josephbakarji/Gluvn/docs/gluvn_dataflow.pdf

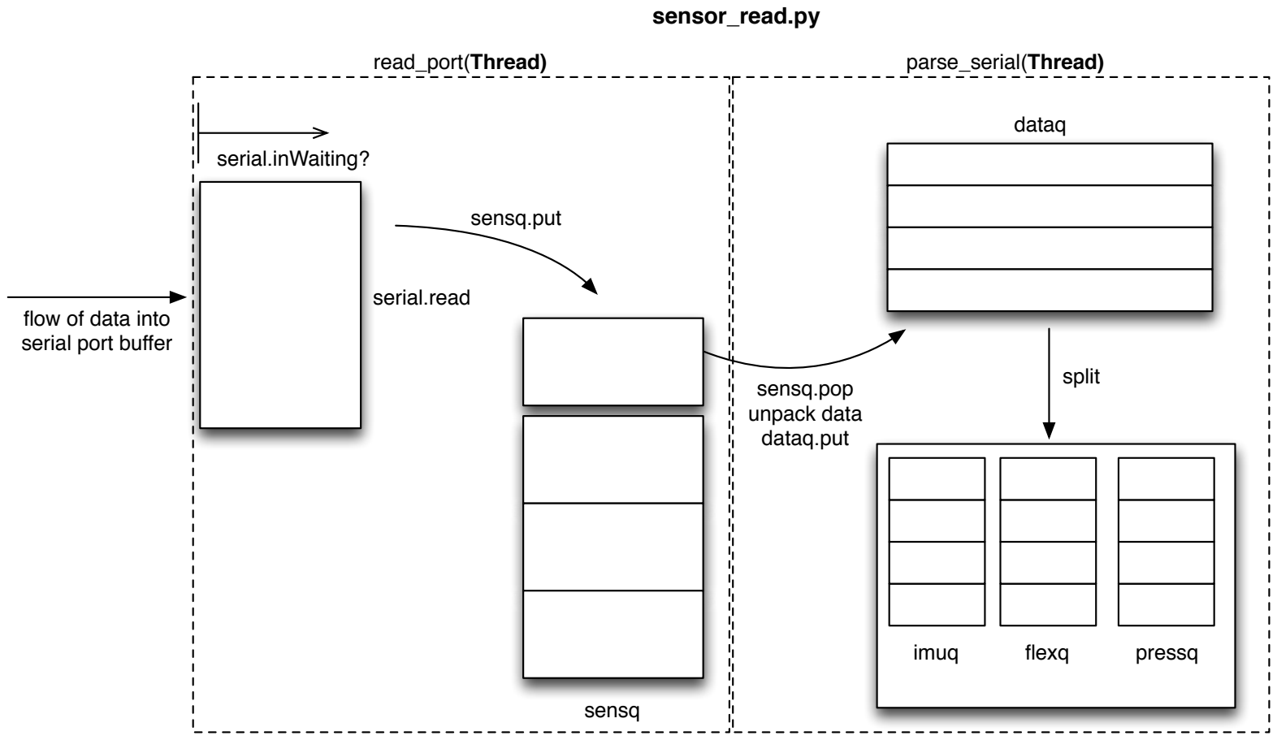
[picture p6: page 1]

flow of data into
serial port buffer

serial.read

sensq.put

sensq

dataq

imuq | flexq | pressq

sensq.pop
unpack data
dataq.put

split

read_port(Thread) | parse_serial(Thread)

sensor_read.py

serial.inWaiting?
