josephbakarji/Gluvn/docs/m5stick_dimensions.png

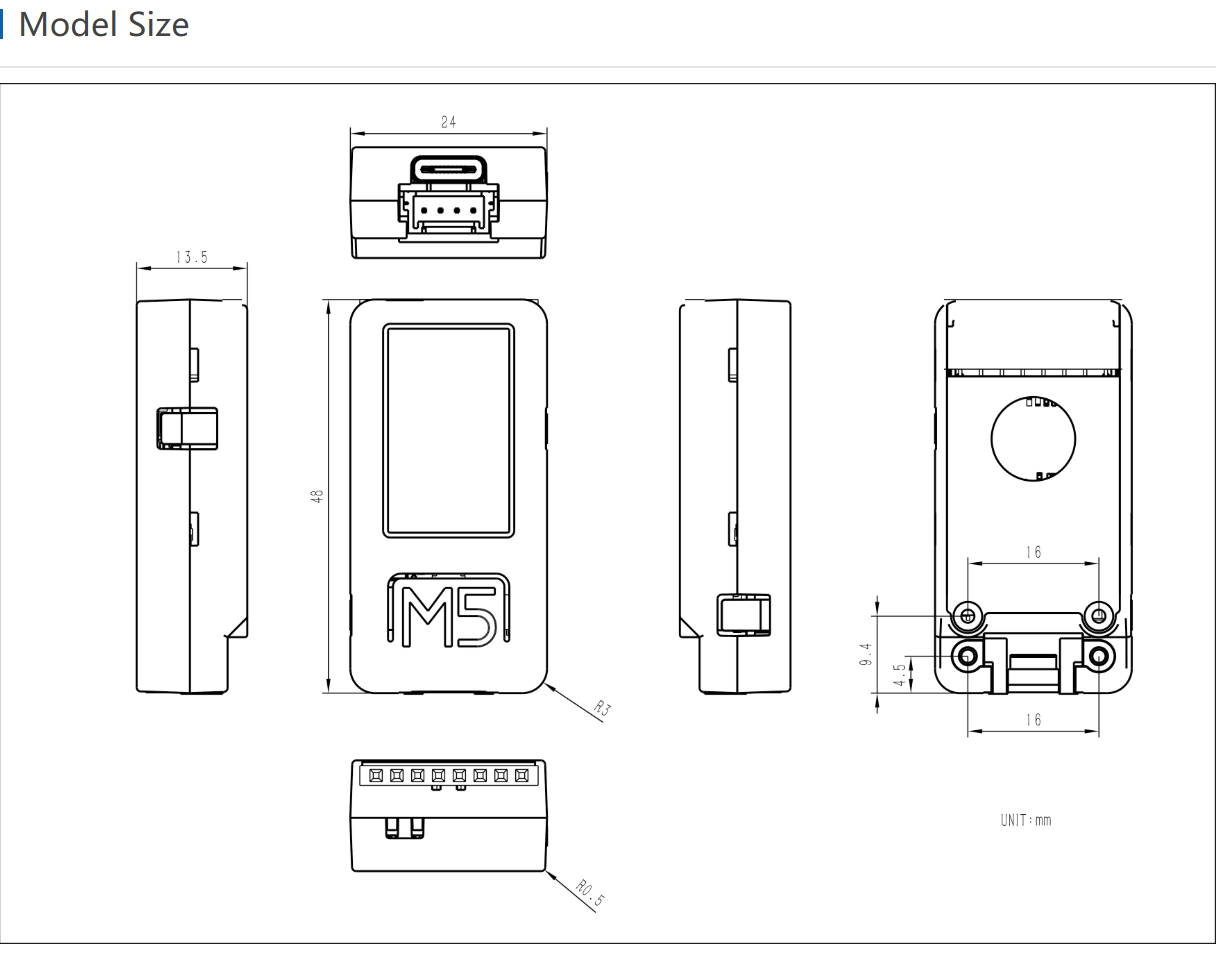
docs/m5stick_dimensions.png
