josephbakarji/Gluvn/hardware/docs/m5stick_dimensions.png

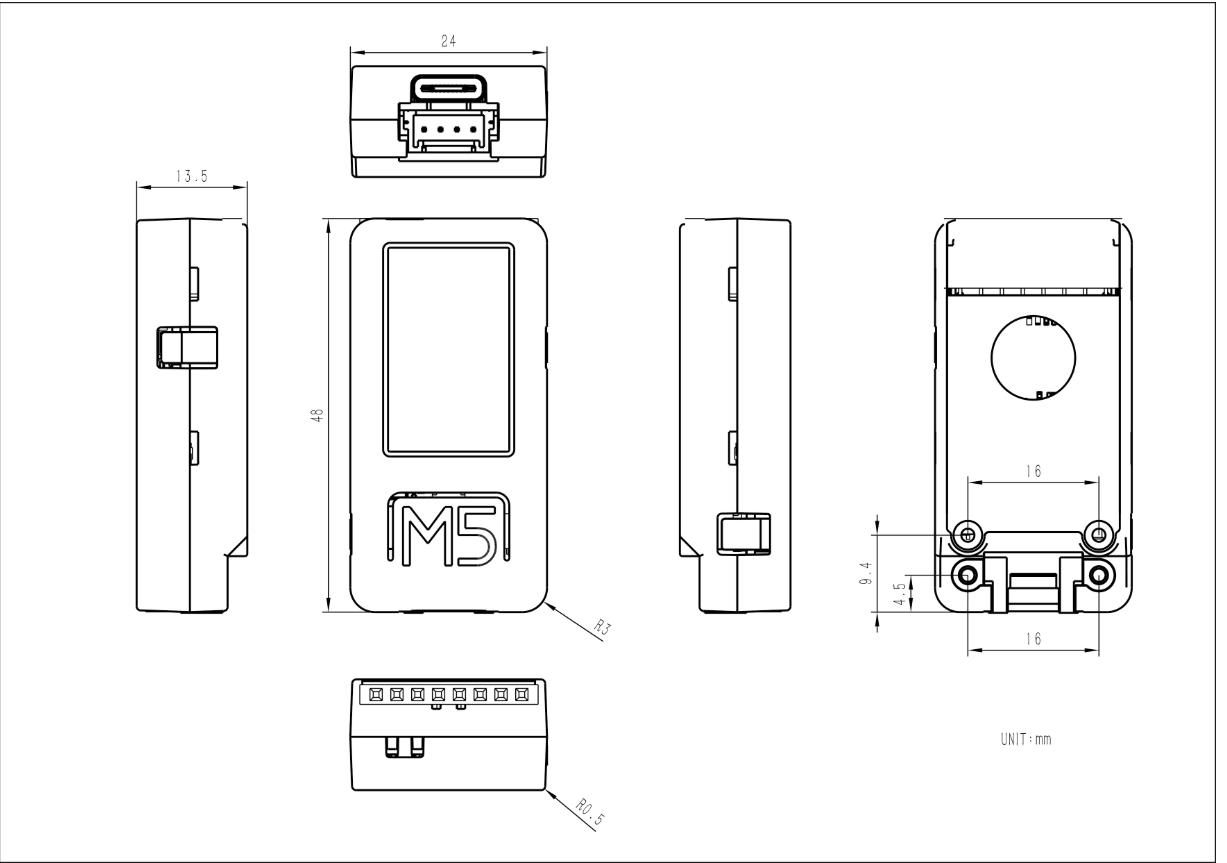
hardware/docs/m5stick_dimensions.png
