josephbakarji/Gluvn/hardware/images/PCB/2D-Top-Layer.png

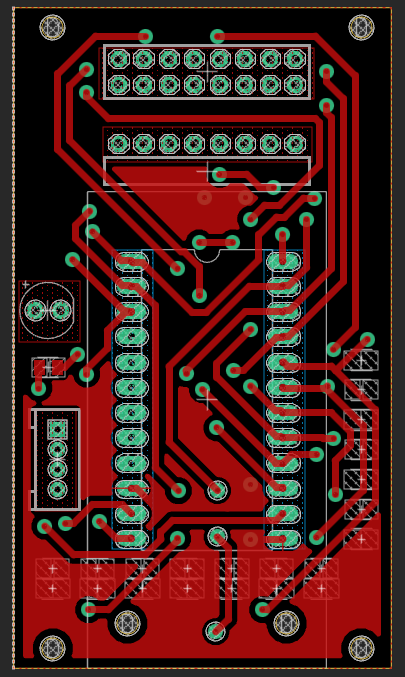
hardware/images/PCB/2D-Top-Layer.png
