josephbakarji/Gluvn/hardware/images/PCB/Final_PCB_Bottom.jpg

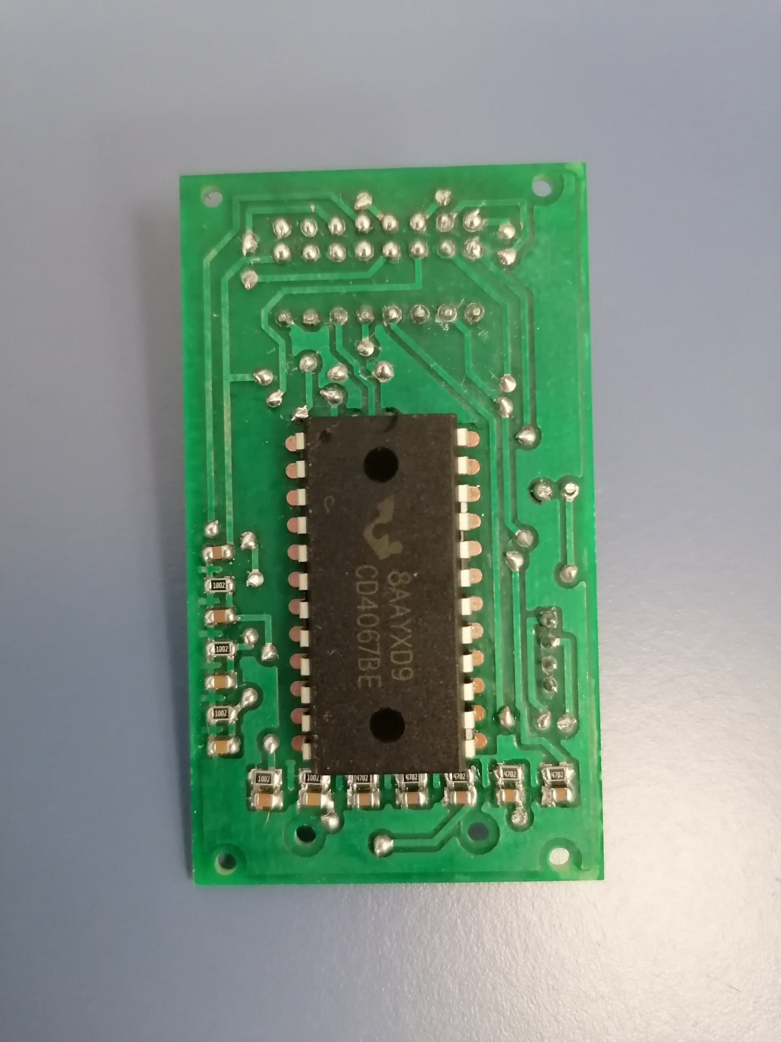
hardware/images/PCB/Final_PCB_Bottom.jpg
