josephbakarji/Gluvn/hardware/images/PCB/Final_PCB_Top.jpg

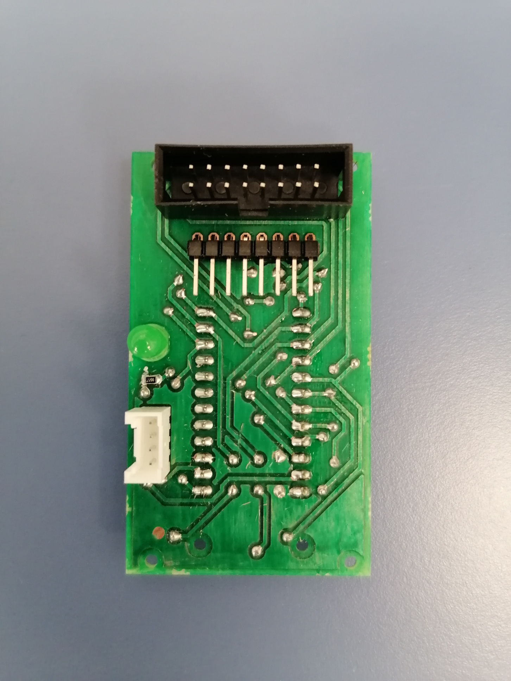
hardware/images/PCB/Final_PCB_Top.jpg
