josephbakarji/Gluvn/hardware/images/Enclosure_box/Enclosure_Assembly_Bottom.png

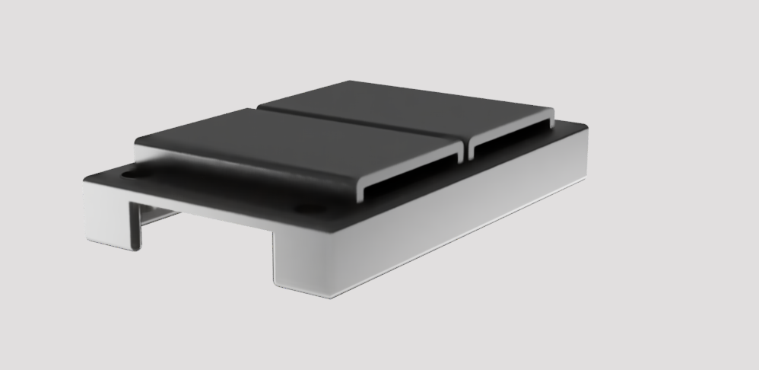
hardware/images/Enclosure_box/Enclosure_Assembly_Bottom.png
