josephbakarji/Gluvn/hardware/images/Enclosure_box/Enclosure_Assembly_Top.png

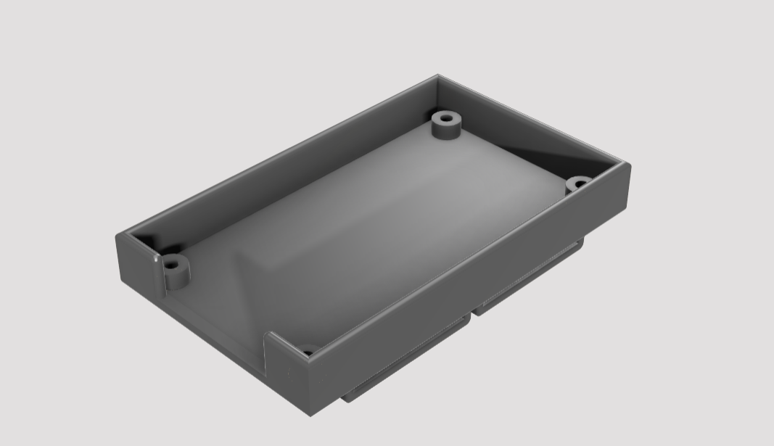
hardware/images/Enclosure_box/Enclosure_Assembly_Top.png
