josephbakarji/Gluvn/hardware/images/Enclosure_box/Printed box Bottom.jpg

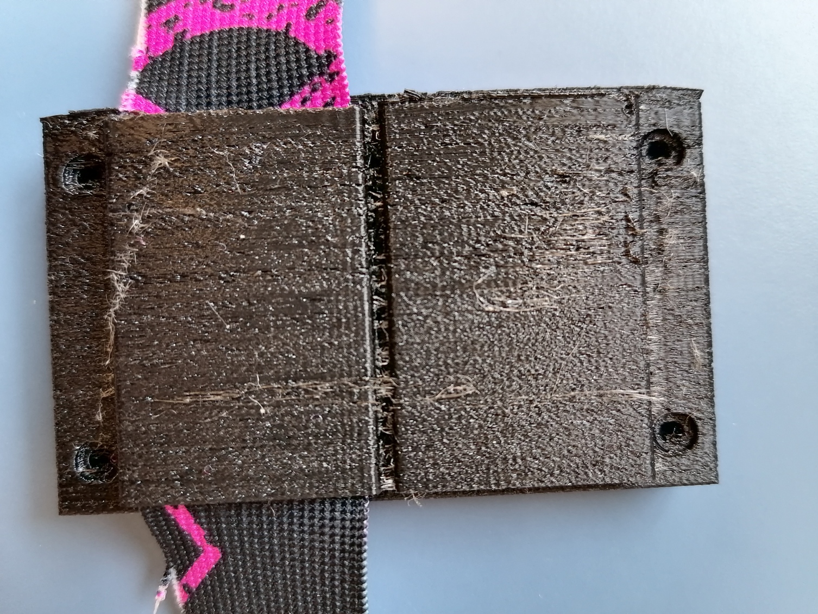
hardware/images/Enclosure_box/Printed box Bottom.jpg
