josephbakarji/Gluvn/hardware/images/Enclosure_box/Printed box Top.jpg

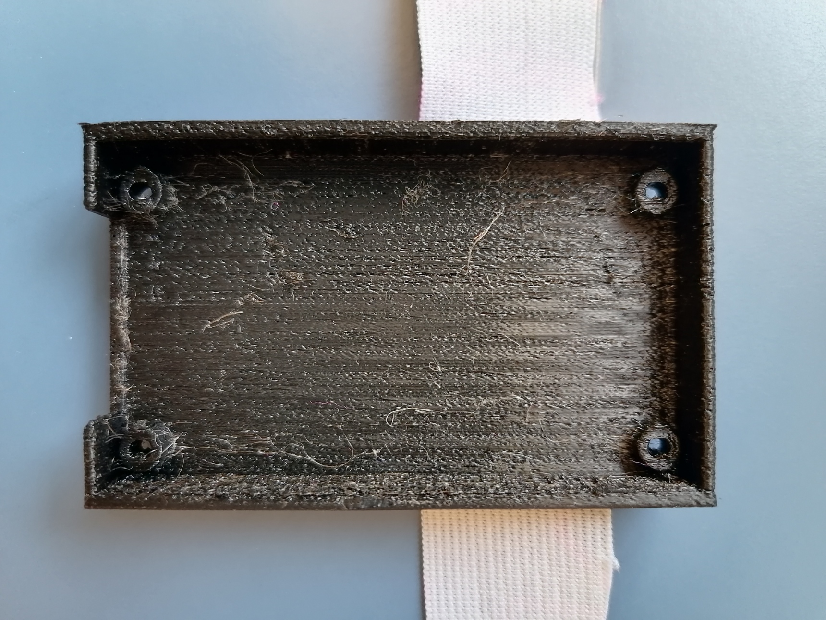
hardware/images/Enclosure_box/Printed box Top.jpg
