josephbakarji/Gluvn/hardware/images/Full setup/Glove_exterior.jpg

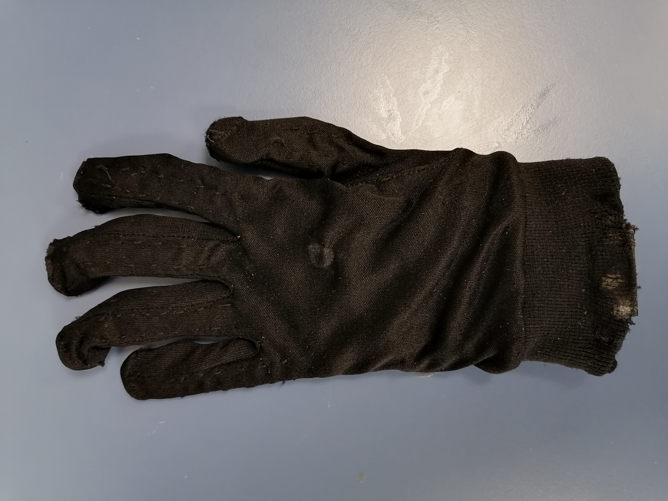
hardware/images/Full setup/Glove_exterior.jpg
