josephbakarji/Gluvn/hardware/images/Full setup/Glove_interior.jpg

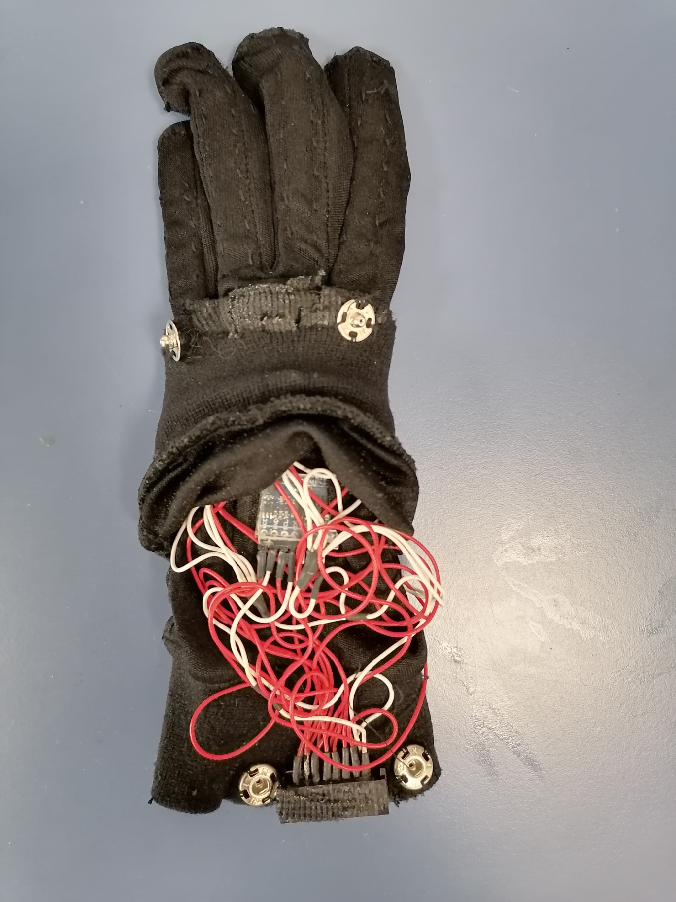
hardware/images/Full setup/Glove_interior.jpg
