josephbakarji/Gluvn/hardware/images/Full setup/PCB_Enclosure_SideView1.jpg

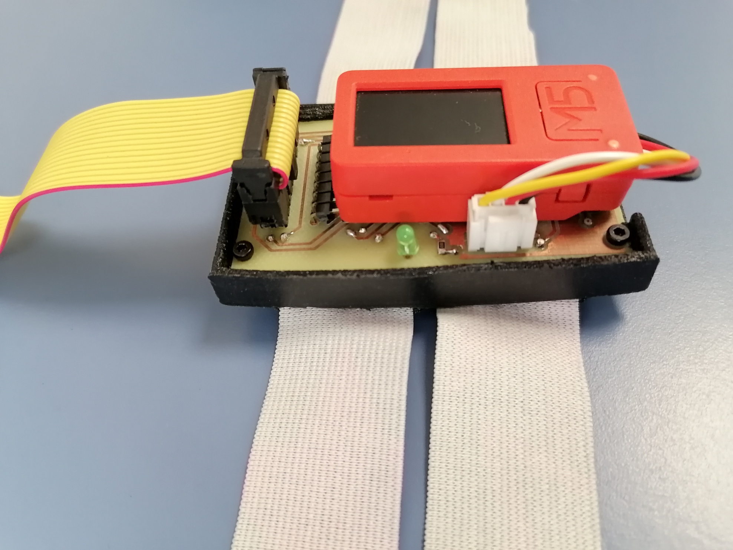
hardware/images/Full setup/PCB_Enclosure_SideView1.jpg
