josephbakarji/Gluvn/hardware/images/Full setup/PCB_Enclosure_SideView2.jpg

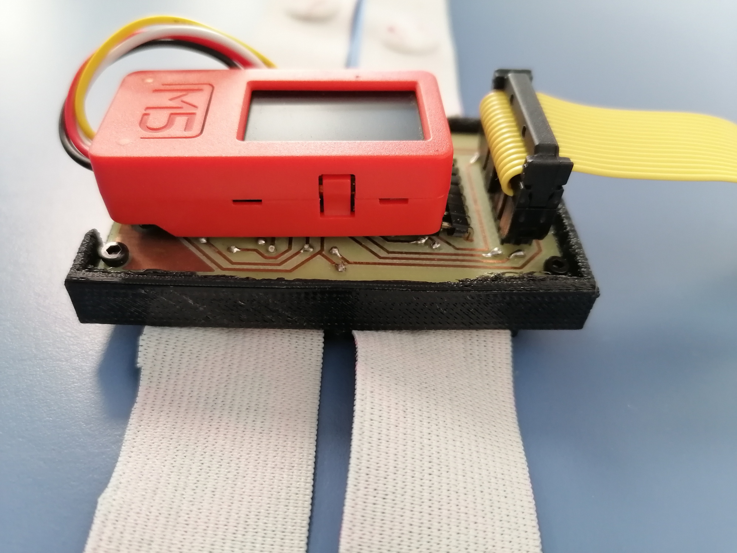
hardware/images/Full setup/PCB_Enclosure_SideView2.jpg
