josephbakarji/Gluvn/hardware/images/Full setup/PCB_Enclosure_TopView.jpg

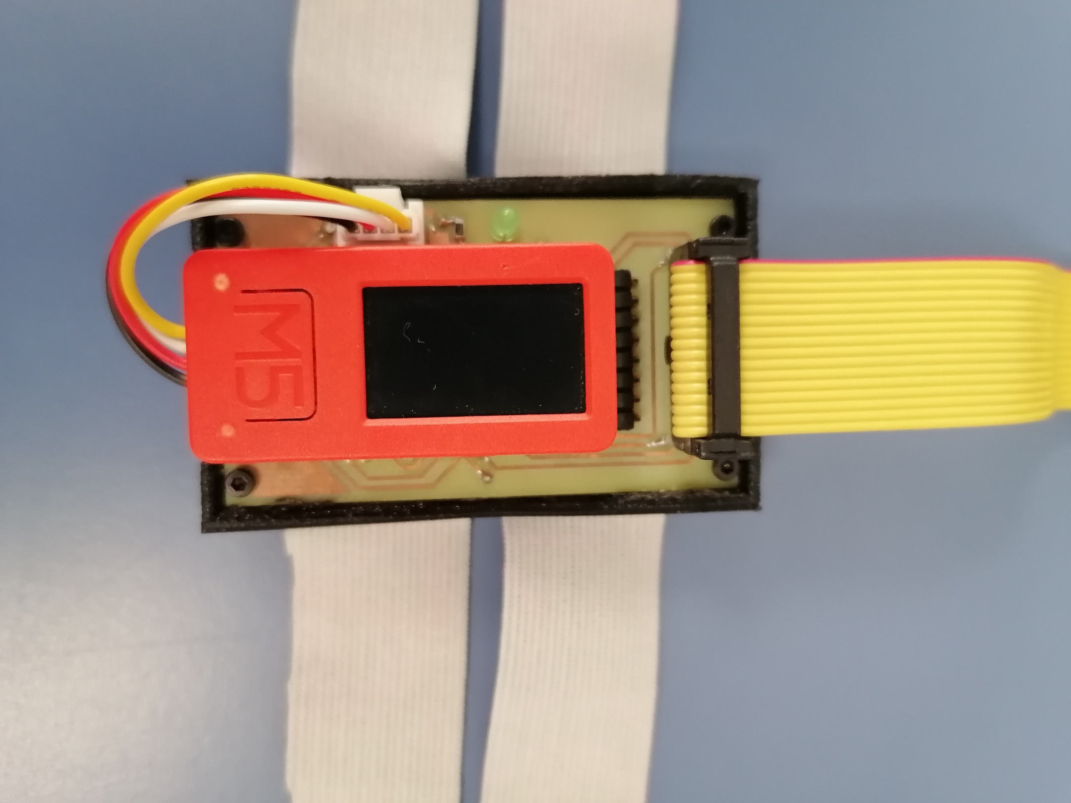
hardware/images/Full setup/PCB_Enclosure_TopView.jpg
