josephbakarji/Gluvn/software_python/figures/benchmark_results.png

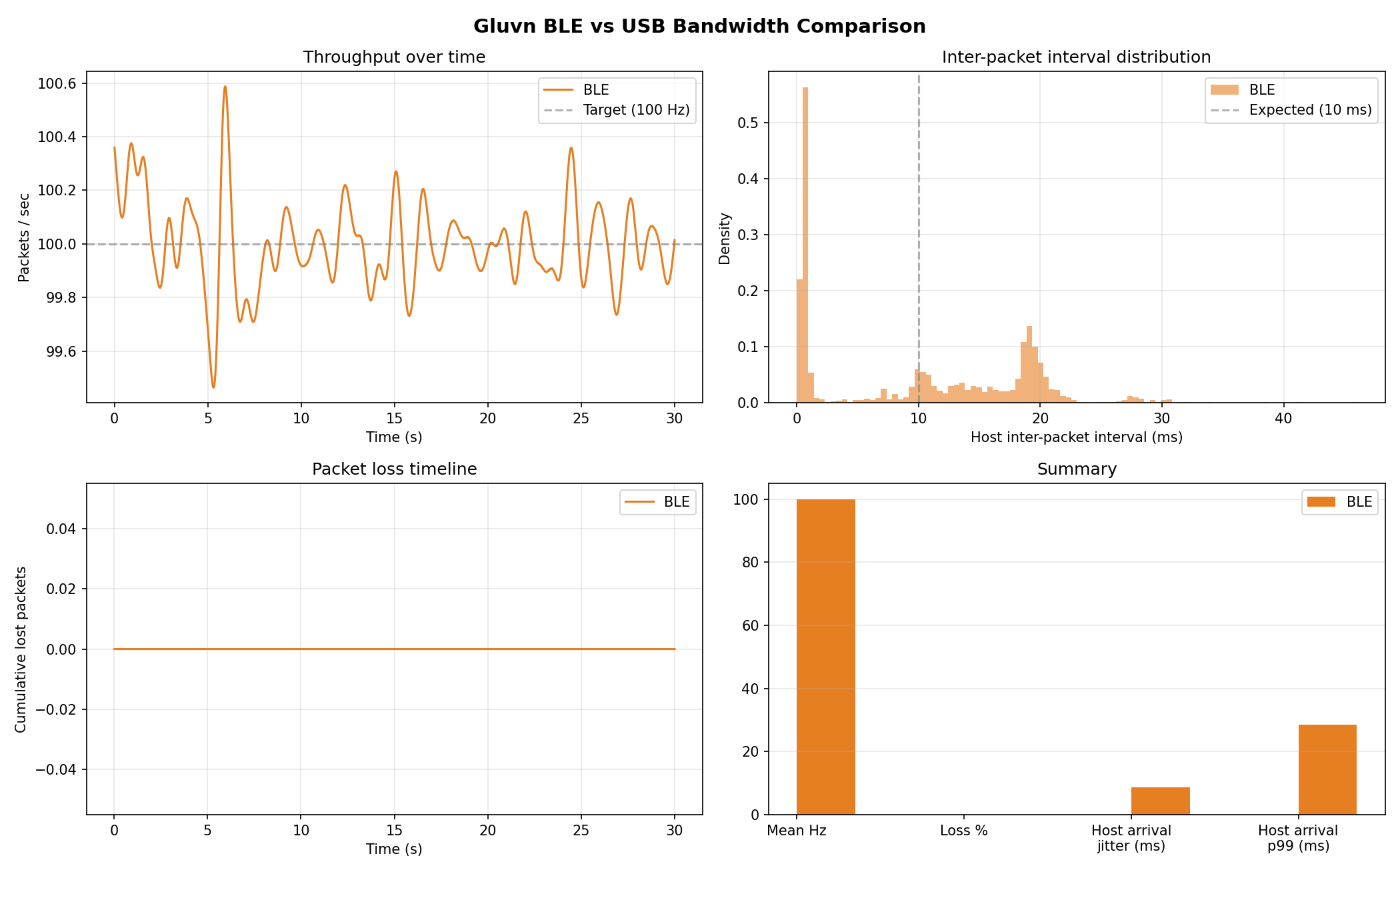
software_python/figures/benchmark_results.png
