josephbakarji/Gluvn/software_python/figures/IMU/mahony_validation_20260812_075407_USB.png

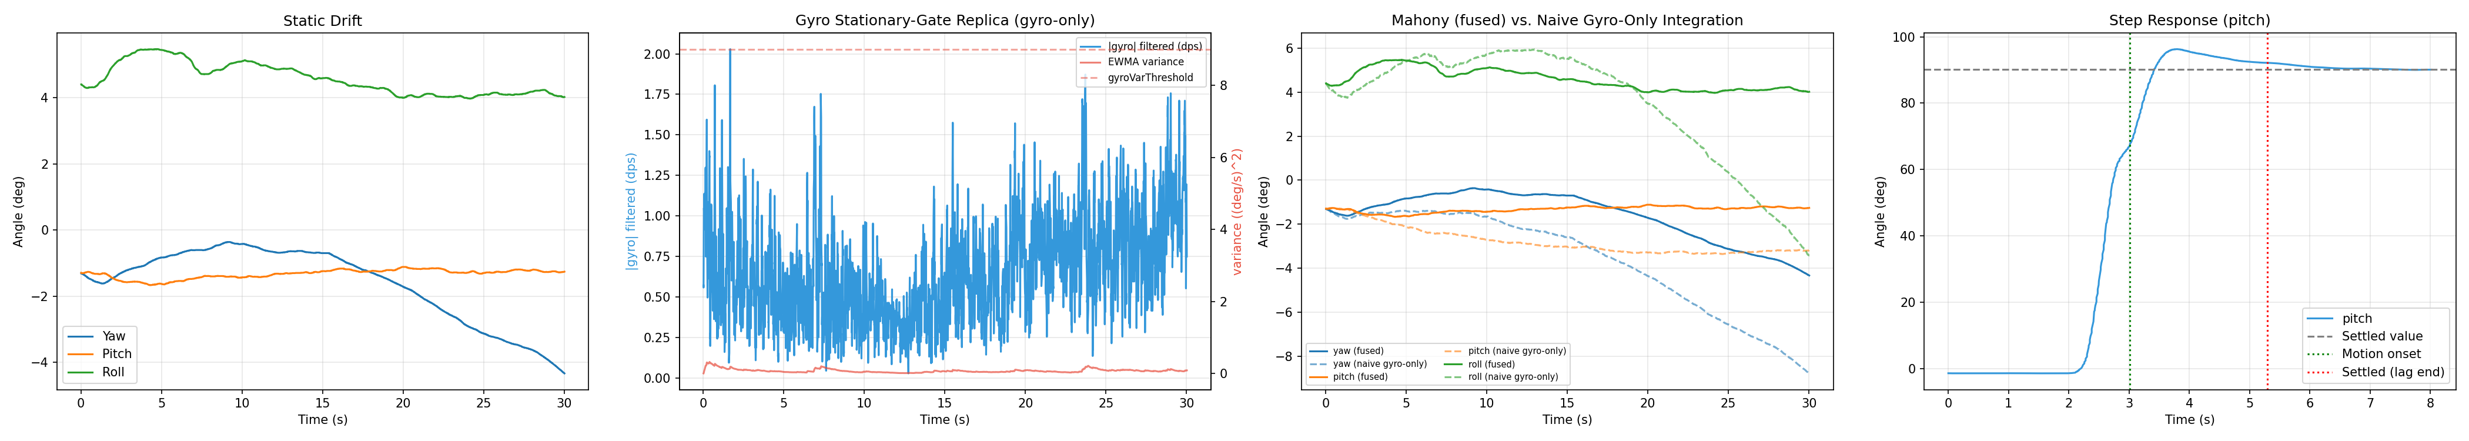
software_python/figures/IMU/mahony_validation_20260812_075407_USB.png
