josephbakarji/Gluvn/software_python/figures/IMU/mahony_validation_20260812_075737_USB.png

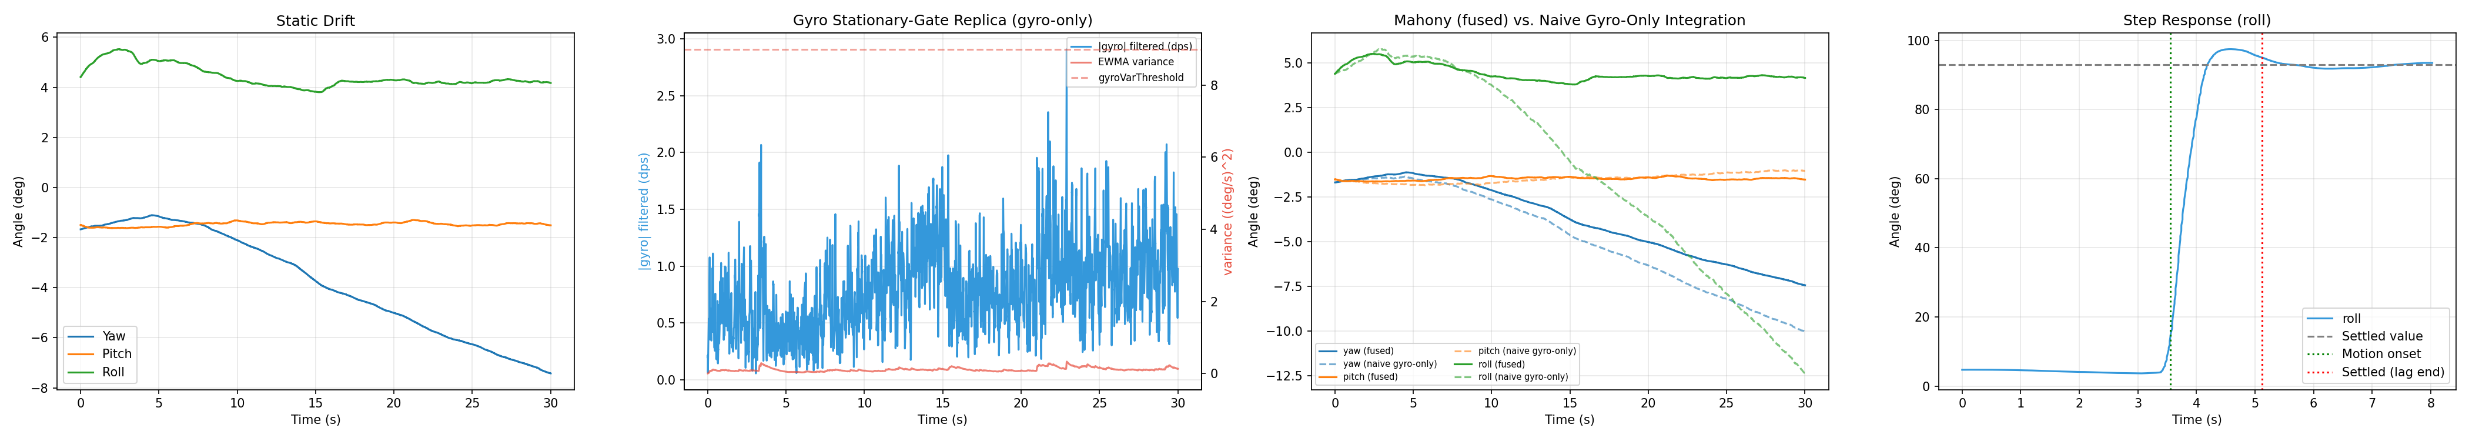
software_python/figures/IMU/mahony_validation_20260812_075737_USB.png
