josephbakarji/Gluvn/software_python/tests/testfiles/readmidi_test/test0.logicx/Alternatives/000/WindowImage.jpg

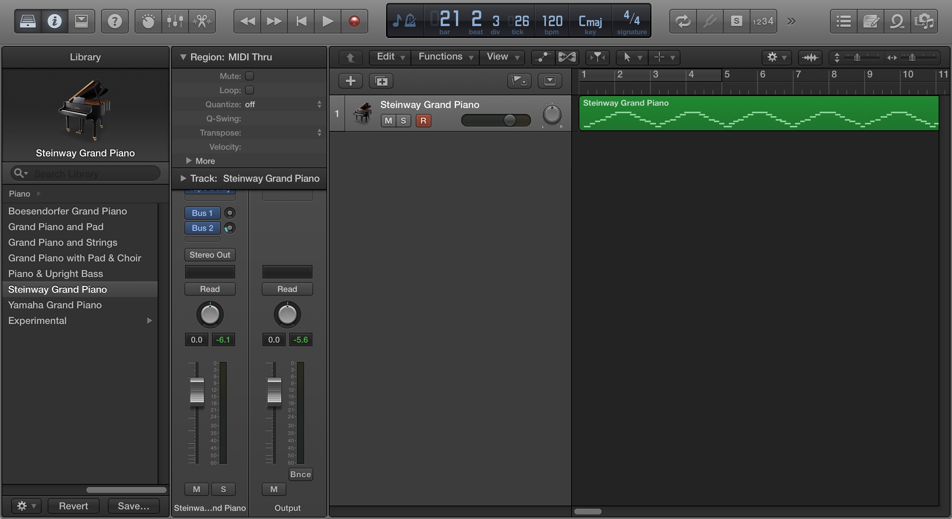
software_python/tests/testfiles/readmidi_test/test0.logicx/Alternatives/000/WindowImage.jpg
