josephbakarji/Gluvn/software_python/figures/all_sensors.pdf

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

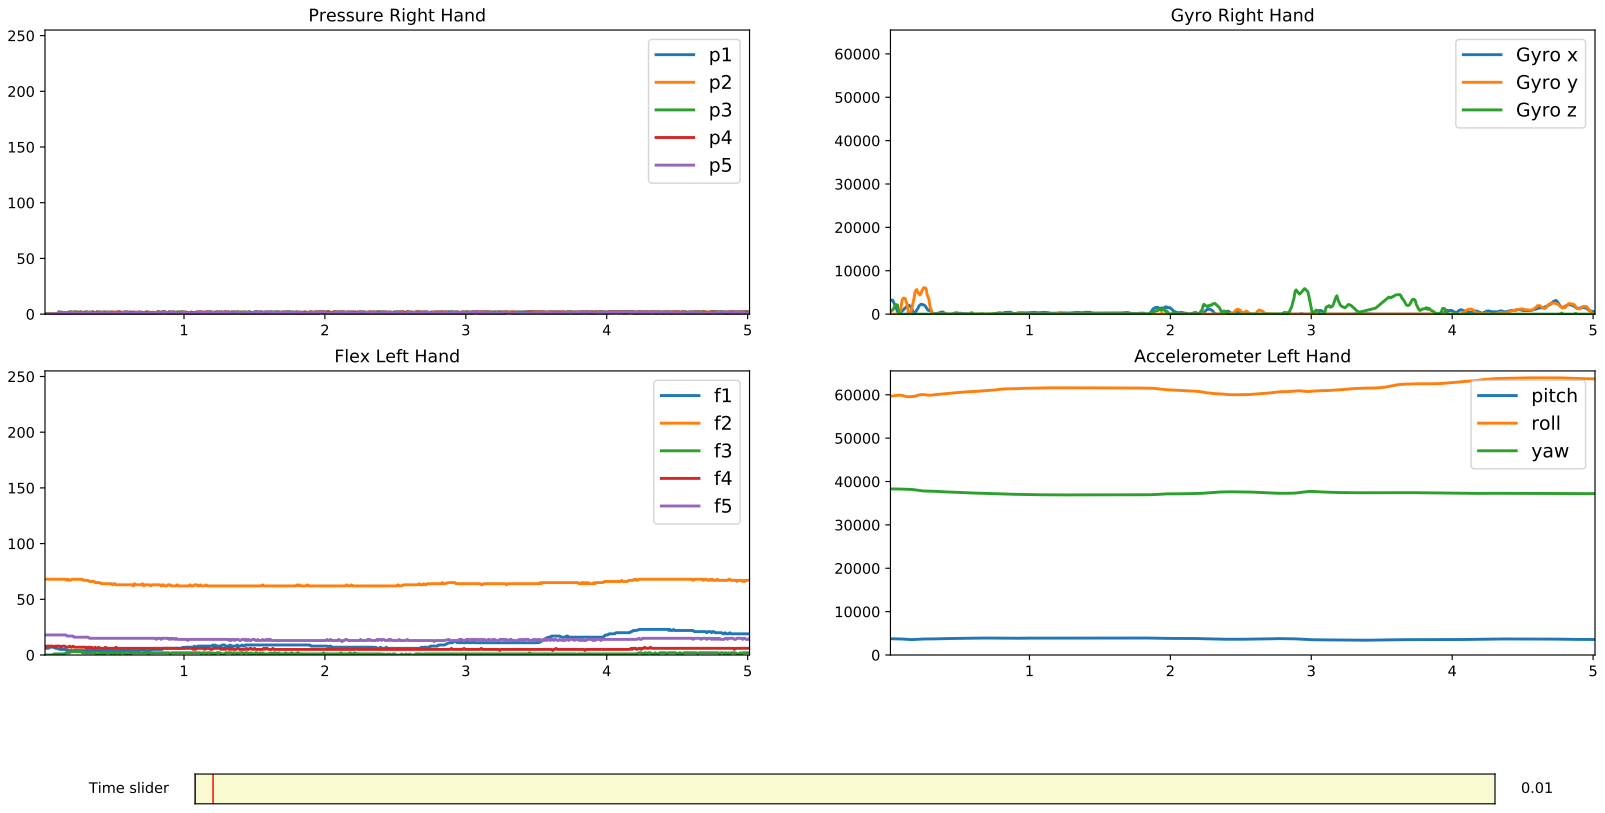
[picture p42: page 1]
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
