josephbakarji/Gluvn/software_python/figures/notes_and_sensors.pdf

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

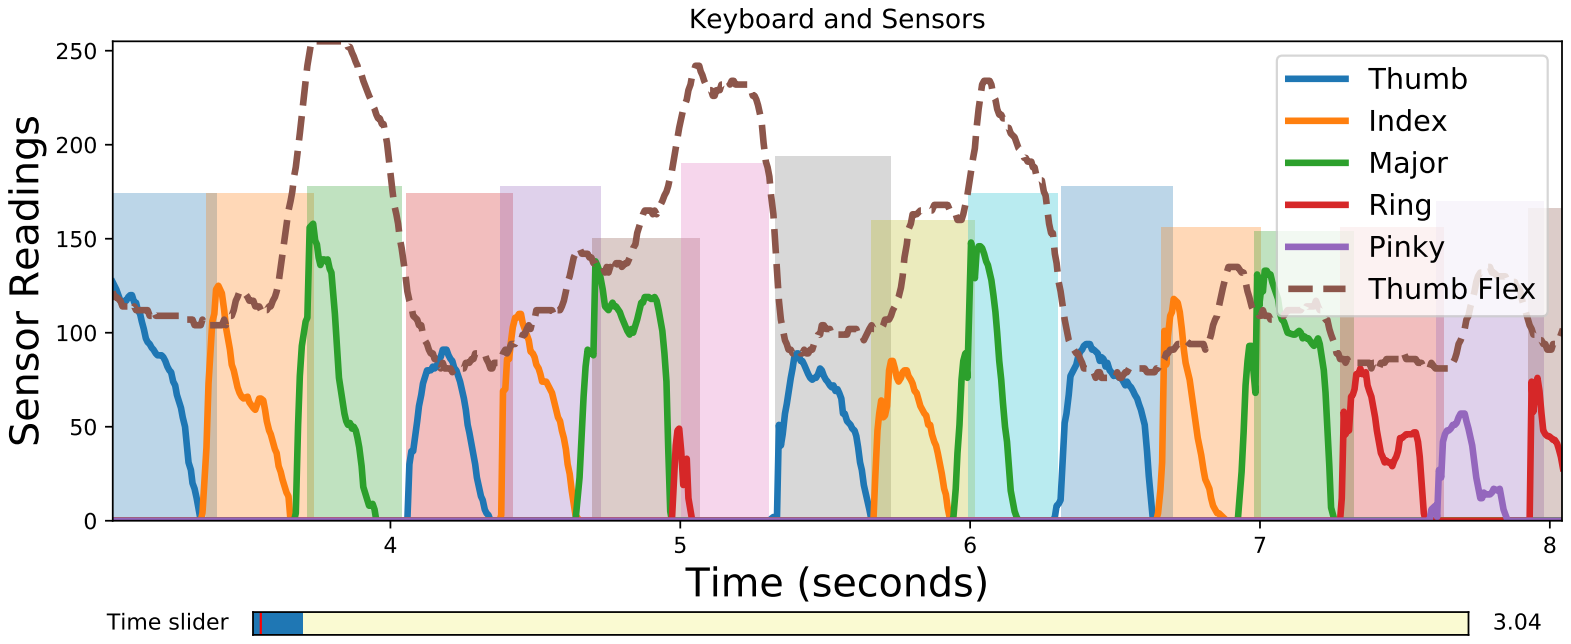
[picture p43: page 1]
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
