josephbakarji/Gluvn/firmware/m5stick_firmware/calibration.h

#ifndef CALIBRATION_H
#define CALIBRATION_H

int R_MIN_FLEX[]  = {970, 2142, 1712, 2124, 1609};
int R_MAX_FLEX[]  = {564, 1117, 848, 1060, 616};
int R_MIN_PRESS[] = {0, 0, 0, 0, 0};
int R_MAX_PRESS[] = {2267, 3129, 3191, 2972, 2791};

int L_MIN_FLEX[]  = {1492, 1053, 1805, 1974, 1691};
int L_MAX_FLEX[]  = {1080, 403, 1061, 954, 669};
int L_MIN_PRESS[] = {0, 0, 0, 0, 0};
int L_MAX_PRESS[] = {2269, 3587, 2820, 3275, 1435};

#endif
